mberthod/noisyless/01_PROJETS/202604_089_Capteur_Environnemental_V1/04_FABRICATION/PXL_20250319_190052271.MP.jpg

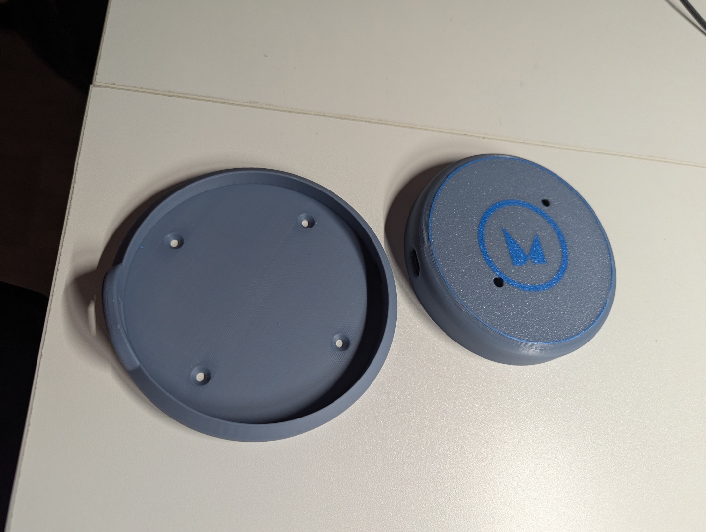
01_PROJETS/202604_089_Capteur_Environnemental_V1/04_FABRICATION/PXL_20250319_190052271.MP.jpg
