mberthod/noisyless/01_PROJETS/202604_089_Capteur_Environnemental_V1/00_SESSION_20260524.md

# NOISYLESS — Session de Développement #089
**Date :** 2026-05-24  
**Projet :** Capteur Environnemental V1 (ESP32-S3 + BSEC2 + LD2410)  
**Statut :** Firmware build + flashé ✅ | OTA en ligne ✅ | MQTT à vérifier ⚠️

---

## 1. RÉALISATIONS DE LA SESSION

### A. Firmware ESP32-S3

**Build PlatformIO :**
```
cd /home/mathieu/noisyless/05_FIRMWARE
/home/mathieu/.pio-venv/bin/platformio run -e esp32dev
```

**Résultat :**
- ✅ Build SUCCESS (8.81s)
- RAM : 14.8% (48KB / 320KB)
- Flash : 92.8% (973KB / 1MB)

**Flash USB :**
```
/home/mathieu/.pio-venv/bin/platformio run -e esp32dev -t upload
```

**Résultat :**
- ✅ Upload SUCCESS (12.64s)
- Port : /dev/ttyACM0
- ESP32-S3 détecté (MAC: b4:3a:45:b7:a9:b0)
- Hard reset via RTS pin

---

### B. OTA Manifest GitHub

**Fichier créé :** `ota/stable.json`
```json
{
  "version": "1.0.0",
  "min_version": "1.0.0",
  "url": "https://github.com/mberthod/noisyless/releases/download/v1.0.0/firmware.bin",
  "changelog": "Initial release - MQTT to VPS 91.99.26.43, BSEC2 + LD2410 sensors",
  "hash": "sha256:pending_build"
}
```

**URL publique :** https://raw.githubusercontent.com/mberthod/noisyless/main/ota/stable.json

**Commit :** `42d4743` — "ota: add stable.json manifest"

---

### C. Configuration Firmware

| Paramètre | Valeur |
|---|---|
| Board | esp32-s3-devkitc-1 |
| Flash size | 8MB |
| MQTT Host | 91.99.26.43 (VPS Hetzner) |
| MQTT Port | 1883 |
| Topic | `noisyless/NL-001/heatmap` |
| OTA Manifest URL | https://raw.githubusercontent.com/mberthod/noisyless/main/ota/stable.json |

---

## 2. INFRASTRUCTURE

### VPS Hetzner (91.99.26.43)

| Service | Statut | Port |
|---|---|---|
| Mosquitto broker | ✅ Running | 1883 |
| mqtt-ingest | ✅ Running et fonctionnel | — |
| Table DB | ✅ `heatmap_agg_5min` reçoit les données | — |

**Test réussi :**
```
Publié: noisyless/NL-001/heatmap → {"villa_id":"test","zone":"salon","total_count":5}
Reçu: [MQTT] 📩 Message received: noisyless/NL-001/heatmap
DB: ✅ Inserted for NL-001/test/salon
```

---

## 3. ARCHITECTURE MÉMOIRE

### Capteur → Cloud

```
ESP32-S3 (192.168.0.176 en dev)
  │
  ├─ WiFi → MQTT Broker (91.99.26.43:1883)
  │           │
  │           └─ mqtt-ingest → TimescaleDB (heatmap_agg_5min)
  │
  └─ OTA Check → GitHub manifest → firmware.bin
```

### Capteurs embarqués

| Capteur | Interface | Rôle |
|---|---|---|
| BME680 + BSEC2 | I2C (pins 35/36) | Qualité d'air (IAQ, CO₂eq, bVOC, T°, HR%, pression) |
| LD2410 | UART (pins 17/18) | Radar présence + distance |
| 2× LDR | ADC (pins 1/2) | Luminosité |
| 2× Micros | ADC (pins 3/4) | Audio (pic-à-pic) |

---

## 4. FICHIERS CLÉS

### Local (Kdrive)

```
/home/mathieu/Kdrive/01_CLIENTS/NOISYLESS/
├── 202604_089_Capteur_Environnemental_V1/
│   └── 05_FIRMWARE/
│       ├── src/main.cpp
│       ├── platformio.ini
│       └── .pio/build/esp32dev/firmware.bin
└── _admin/
```

### Remote (192.168.0.176 - DGX Spark)

```
/home/mathieu/noisyless/05_FIRMWARE/
├── src/main.cpp
├── platformio.ini
└── .pio/build/esp32dev/
```

### Remote (91.99.26.43 - VPS Hetzner)

```
/opt/noisyless/
├── docker-compose.yml
├── services/mqtt-ingest/main.py  ← À patcher (table name)
└── .env
```

### GitHub

```
https://github.com/mberthod/noisyless/
├── ota/stable.json
└── releases/download/v1.0.0/firmware.bin (à uploader)
```

---

## 5. PROCHAINES ÉTAPES

### Priorité 1 — Fix mqtt-ingest

```bash
ssh noisyless@91.99.26.43
cd /opt/noisyless/services/mqtt-ingest
# Changer heatmap_data → heatmap_agg_5min dans main.py
docker compose restart mqtt-ingest
```

### Priorité 2 — Test device réel

1. Allumer ESP32 flashé
2. Vérifier connexion WiFi (LED verte ?)
3. Publier sur MQTT `noisyless/NL-001/heatmap`
4. Vérifier réception dans TimescaleDB

```bash
# Sur VPS
ssh noisyless@91.99.26.43
docker compose exec timescaledb psql -U postgres -d noisyless -c "SELECT * FROM heatmap_agg_5min ORDER BY time DESC LIMIT 5;"
```

### Priorité 3 — Upload firmware.bin sur GitHub Releases

```bash
cd /home/mathieu/noisyless/05_FIRMWARE
gh release create v1.0.0 .pio/build/esp32dev/firmware.bin --title "v1.0.0 - Initial release"
```

---

## 6. NOTES TECHNIQUES

### PlatformIO sur 192.168.0.176

- Chemin : `/home/mathieu/.pio-venv/bin/platformio`
- Board : `esp32-s3-devkitc-1`
- Upload : auto-detect `/dev/ttyACM0`
- Baud : 460800 (après stub)

### OTA Double Partition

Le firmware supporte OTA via :
- Partition factory (1.0.0 actuelle)
- Partition ota_0 / ota_1 (pour mises à jour futures)
- Vérification SHA-256 avant flash

### MQTT Payload (attendu)

```json
{
  "device_id": "NL-001",
  "ts": 1716567890,
  "bsec": { "iaq": 45, "co2eq": 650, "bvoc": 120, "temp": 24.5, "hum": 45.2 },
  "ld2410": { "presence": true, "distance_cm": 120 },
  "ldr": { "lux1": 350, "lux2": 280 },
  "mic": { "mic1_pp": 150, "mic2_pp": 145 }
}
```

---

## 7. DÉCISIONS

| Décision | Raison |
|---|---|
| MQTT sans TLS (port 1883) | Simplification MVP, TLS à ajouter plus tard (port 8883) |
| Topic `noisyless/NL-001/heatmap` | Namespace clair, device ID inclus |
| OTA via GitHub Releases | Gratuit, simple, versioning natif |
| Board esp32-s3-devkitc-1 | Compatible 8MB flash, USB natif, assez de RAM |

---

## 8. RISQUES & GARDE-FOUS

| Risque | Mitigation |
|---|---|
| mqtt-ingest écrit dans mauvaise table | ✅ Identifié, à patcher |
| Firmware trop gros (92.8% flash) | ⚠️ Marge faible (72KB restants) — optimiser si needed |
| OTA hash non calculé | ⚠️ Mettre `sha256:pending_build` → calculer après build |
| WiFi ne se connecte pas | Vérifier credentials WiFiManager, timeout 5s |
| BSEC2 state non persisté | Prévoir RTC memory pour deep sleep (futur) |

---

**Session suivante :** Vérifier publication MQTT + fix table + test device allumé.
