mberthod/noisyless/.hermes/backlog/logs/2026-05-24_1519_fw-06.md

# Log fw-06 — 2026-05-24 15:19

**Tâche** : Créer la structure du firmware node-radar-60ghz : CMakeLists.txt, main/, components/

**Fichiers créés** :
- `firmware/node-radar-60ghz/CMakeLists.txt` — Projet ESP-IDF, EXTRA_COMPONENT_DIRS → components/
- `firmware/node-radar-60ghz/main/main.c` — Skeleton avec 3 tâches FreeRTOS (sensor_task, health_task, master_task), init NVS/netif/event-loop, timer périodique 1s, pins LED/ADC
- `firmware/node-radar-60ghz/main/CMakeLists.txt` — Composant ESP-IDF standard
- `firmware/node-radar-60ghz/components/` — Dossier vide, prêt pour ld6001a, mesh, config

**Détails main.c** :
- Inclusions complètes : freertos, esp_log, nvs_flash, esp_netif, esp_event, driver/gpio, driver/adc
- TODO placés stratégiquement aux points d'insertion pour ld6001a.h, mesh.h, config.h
- sensor_task : structure de lecture radar UART avec TODO pour ld6001a_read_frame()
- health_task : lecture ADC batterie, seuil critique 3000mV → deep sleep 10min
- master_task : skeleton avec TODO mesh_get_role() et fusion/publish MQTT
- app_main() : init LED, NVS, TCP/IP, crée les 3 tâches pinned core 0, timer 1s

**Modèle utilisé** : node-tof-esp32s3/main/main.c — mêmes tâches mais adapté pour radar (UART au lieu d'I²C, pas de grille ToF)

**Résultat** : ✅ Structure créée, 3 fichiers + dossier components vide. Prêt pour fw-07 (remplir main.c après drivers).
