mberthod/noisyless/.hermes/backlog/logs/2026-05-24_fw-01.md

# Log — fw-01 — 2026-05-24

## Tâche
**ID** : fw-01  
**Goal** : Tester le deep sleep sur le firmware #089  
**Priorité** : 3  

## Statut final
**BLOCKED** → Hardware ESP32-S3 non disponible.

## Raison
Le test de deep sleep nécessite :
- Une carte ESP32-S3 physique à flasher
- Un multimètre/analyseur de consommation pour mesurer la conso deep sleep (<100µA)
- Le firmware #089 prêt à être flashé

Hermes ne peut pas flasher physiquement ni mesurer la consommation réelle.

## Actions effectuées
- Tâche marquée `blocked` dans todo.json.

## Prochaine étape
Mathieu doit fournir le matériel et flasher manuellement.
