mberthod/noisyless/01_PROJETS/202604_089_Capteur_Environnemental_V1/01_CAHIER_DES_CHARGES/Cahiers des charges.odt

Cahiers des charges

# Objectifs du produit

Permettre de monitorer dans une location courte durée les différents paramètres environnementaux :

Parametre | objectif/explication | unité | Affichage ecran
Température | Indispensable pour le confort intérieur | mesuré en °C | oui
Humidité | Important pour le confort et le risque de croissance de moisissures | RH % | oui
Pression de l'air | En corrélation avec les changements météorologiques | Pa | oui
Résistance du capteur de gaz | Réagit aux impuretés chimiques organiques volatiles (COV) présentes dans l'air | ppm | oui
Indice de qualité de l'air | Combine le gaz, la température et l’humidité dans une évaluation de la qualité de l’air | Bon, moyen, mauvais | oui
Pression acoustique pondérée A | Niveau de pression acoustique (SPL) adapté à l'audition humaine | dB | non
Bande de fréquence SPL (x6) | Niveau de pression acoustique pour 6 bandes de fréquences, de 88 Hz à 5600 Hz | dB | non
Amplitude sonore maximale | La valeur en db des sons impulsifs soudains | dB | non
Éclairement | Luminosité totale, adaptée à la vision humaine | Lux | non
Niveau de lumière blanche | Luminosité totale sur toutes les longueurs d'onde mesurées | Lux | non

# Fonctionnement

le capteur est placé dans la ou les pièces du logement branché sur secteur

se connecte en wifi sur la box du logement ( a voir pour connexion 4G)

envoi sur le serveur de manière periodique les éléments le serveur gère les alertes

## Possibilités futures :

connexion 4G

fonctionnement sur batterie

Panneau de contrôle pour GAZ et qualité de l’air température avec un écran.

Ajout d’un carte micro sd pour logger les éléments en cas de coupure réseau et même coupure courant

# Block diagram

ALIMENTATION 230/5V ESP32 CAPTEUR BME680 - TEMPERATURE, HUMIDITE, PRESSION GAZ VEML6030 Ambient Light Sensor SPH0645LM4H-B MICROPHONE CHARGEUR BATTERIE ECRAN MODEM 4G SD CARD

# Budget électronique

Élément | Prix unitaire | Quantité
esp32S3 | 2,16 | 1
SPH0645LM4H-B | 1,5 | 1
BME680 | 7,4 | 1
VEML6030 | 1,20 | 1
Alimentation 85-240AC - 5VDC | 3 | 1
Écran | 3 | 1
Chargeur de batterie | 1 | 1
Batterie 500mA | 5 | 1
PCB | 5 | 1
| 38€

Version basique : 21€

Version haut de gamme : 31€

prix non optimisée en prod le prix sera inférieur

# Type de boîtier

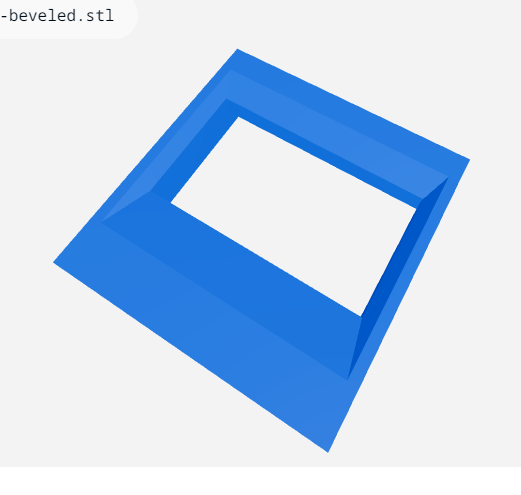
[picture p3: figure]
