mberthod/noisyless/.hermes/backlog/logs/2026-05-24_1545_web-02.md

# Log — web-02 — merci.html
**Timestamp**: 2026-05-24 15:45
**Tâche**: Créer la page /merci.html (confirmation de commande)
**Agent**: Hermes-MBHREP (orchestrateur backlog)
**Statut**: ✅ done

## Vérification
- Fichier: `/home/mathieu/Kdrive/01_CLIENTS/NOISYLESS/web/site/merci.html`
- Existe: ✅ OUI (87 lignes, 2606 bytes)
- Contenu: conforme au template NEWTODO.md section 1.4
  - `<meta name="robots" content="noindex">` ✅
  - Lecture params URL (name, email, session_id) ✅
  - Affichage dynamique via JS ✅
  - Style centré, simple ✅
  - Bouton "Retour au site" ✅
- Le fichier était déjà créé (probablement par un run précédent ou une création manuelle)

## Actions précises
- Aucune modification nécessaire — le fichier est conforme

## Fichiers modifiés
- Aucun (fichier déjà conforme)

## Résultat
- Tâche marquée "done" dans todo.json
- Page accessible à l'URL prévue
