mberthod/noisyless/.hermes/backlog/logs/2026-05-24_1615_web-03.md

# Log — web-03 : Page /annule.html (paiement annulé)

**Timestamp** : 2026-05-24 16:15 (estimé)
**Tâche** : Créer la page /annule.html (paiement annulé)
**Agent** : Hermes-MBHREP (orchestrateur backlog NOISYLESS)
**Statut** : ✅ Succès

## Actions précises

1. **Lu** `~/.hermes-mbhrep/backlog/todo.json` → détecté web-03 comme première tâche exécutable (priorité 1, status pending, après web-01 et web-02 déjà done)
2. **Marqué** `web-03` comme `in_progress`
3. **Lu** `NEWTODO.md` section 1.5 pour le contenu HTML exact
4. **Créé** le fichier `/home/mathieu/Kdrive/01_CLIENTS/NOISYLESS/web/site/annule.html` :
   - Contenu conforme exactement au template de NEWTODO.md
   - `<title>Paiement annulé | NOISYLESS</title>`
   - `<meta name="robots" content="noindex">` → pas d'indexation
   - Style inline centré, max-width 600px
   - Message : "Le paiement a été annulé. Aucun montant n'a été débité."
   - Lien "← Retour au site" vers `/`
5. **Marqué** `web-03` comme `done`

## Fichiers créés

- `~/Kdrive/01_CLIENTS/NOISYLESS/web/site/annule.html` : 15 lignes, 509 octets

## Résultat

✅ La page `/annule.html` est créée en tant que fichier statique, prête à être servie. Le lien depuis le checkout Stripe (cancel_url) pointera vers cette page.

## Notes

- Aucune dépendance backend, fichier HTML pur
- Le `noindex` empêche l'indexation par les moteurs de recherche
- La page est référencée dans `index.html` via la fonction `startCheckout()` (cancel_url)
