mberthod/noisyless/.hermes/backlog/logs/2026-05-24_1621_api-03.md

# Log — 2026-05-24 16:21 UTC — api-03

## Tâche
**api-03** : Créer le module emails.py pour l'envoi de confirmation de commande via SMTP OVH.

## Contexte
- Serveur : noisyless@91.99.26.43
- Path API : `/opt/noisyless/services/api/` (contexte du Dockerfile)
- SMTP : ssl0.ovh.net:465, user contact@noisyless.com
- Dépendance : api-01 (Stripe webhook) et api-02 (tables orders) déjà faits

## Actions précises

1. **Analyse de l'infra existante**
   - docker-compose.yml : service api dans `/opt/noisyless/services/api/`
   - shop.py existant : checkout + checkout/status, PAS de webhook
   - main.py : inclut auth, devices, shop routers

2. **Création de emails.py** (`/opt/noisyless/services/api/emails.py`)
   - Fonction `send_order_confirmation(email, name, order_id, amount)`
   - SMTP OVH via ssl0.ovh.net:465 (SMTP_SSL)
   - Template HTML avec nom client, order_id raccourci (8 chars), montant en €
   - Variables d'environnement : SMTP_HOST, SMTP_PORT, SMTP_USER, SMTP_PASSWORD, SMTP_FROM

3. **Création de shop_webhook.py** (`/opt/noisyless/services/api/shop_webhook.py`)
   - Endpoint `POST /shop/webhook`
   - Vérification signature Stripe (si STRIPE_WEBHOOK_SECRET configurée)
   - Sur `checkout.session.completed` : extrait email, name, amount → appelle `send_order_confirmation()`
   - Ignore les autres événements

4. **Intégration dans main.py**
   - Ajout `from shop_webhook import router as shop_webhook_router`
   - Ajout `app.include_router(shop_webhook_router)`

5. **Rebuild et déploiement**
   - `docker compose build api` → succès (cache + COPY)
   - `docker compose up -d api` → conteneur redémarré
   - `docker logs noisyless-api --tail 20` → "Application startup complete"

6. **Tests**
   - `/health` → `{"status":"ok","service":"noisyless-api"}`
   - `POST /shop/webhook` (event test) → `{"status":"ignored","event":"test"}`
   - Webhook opérationnel, route enregistrée

## Fichiers modifiés
- **Créé** : `/opt/noisyless/services/api/emails.py` (55 lignes)
- **Créé** : `/opt/noisyless/services/api/shop_webhook.py` (53 lignes)
- **Modifié** : `/opt/noisyless/services/api/main.py` (ajout router shop_webhook)

## Résultat
✅ **SUCCESS** — Module emails.py créé, webhook Stripe intégré avec appel send_order_confirmation, API rebuildée et redémarrée sans erreur.

## Notes
- Le fichier `docker-compose.yml` n'a PAS été modifié (les vars SMTP et STRIPE_WEBHOOK_SECRET sont à ajouter — tâche api-04)
- `send_order_confirmation()` échouera silencieusement si SMTP_PASSWORD n'est pas set (juste un log warning)
- Le chemin correct est `/opt/noisyless/services/api/`, pas `/opt/noisyless/backend/api/` comme indiqué dans NEWTODO.md

## Erreurs
- Le sous-agent initial a cherché au mauvais path (`/opt/noisyless/backend/api/`) → corrigé par l'orchestrateur
- `curl http://localhost/` → 301 redirect vers HTTPS (normal, nginx force HTTPS)
