mberthod/noisyless/.hermes/backlog/logs/2026-05-24_1653_web-05.md

# Backlog NOISYLESS - web-05

## Tâche
Correction de la copie dans `index.html` du site NOISYLESS.

## Actions
1.  **Remplacement du terme 'surpopulation'** : Toutes les occurrences ont été remplacées par 'suroccupation' dans `/home/mathieu/Kdrive/01_CLIENTS/NOISYLESS/web/site/index.html`.
2.  **Correction de caractères corrompus** : Le motif Unicode '识别ables' a été remplacé par 'identifiables' dans `/home/mathieu/Kdrive/01_CLIENTS/NOISYLESS/web/site/index.html`.
3.  **Vérification** : Les modifications ont été vérifiées par `search_files` et les changements semblent cohérents avec le contexte du site.
4.  **Vérification Git diff** : Le répertoire n'est pas un dépôt Git, et la commande `git diff` a échoué en conséquence, mais les modifications ont été appliquées localement.

## Fichiers Modifiés
*   `/home/mathieu/Kdrive/01_CLIENTS/NOISYLESS/web/site/index.html`

## Résultat
L'index.html est correctement mis à jour avec la terminologie standardisée 'suroccupation' et la correction 'identifiables'.

## Erreurs éventuelles
*   `git diff` n'a pas pu être exécuté car le répertoire n'est pas un dépôt Git.

---
Date/Heure : 2026-05-24_1653
Projet : NOISYLESS
Tâche : web-05
