mberthod/noisyless/.hermes/backlog/logs/2026-05-24_1717_web-06.md

# Log web-06 — 2026-05-24 17:17

**Tâche** : Convertir le site one-pager (ancres #) en URLs réelles multi-pages
**Agent** : Sous-agent orchestrateur → finalisé par Hermes-MBHREP
**Statut** : ✅ Succès

## Actions

1. **Lecture** : `index.html` (613 lignes, 36 KB) dans `/home/mathieu/Kdrive/01_CLIENTS/NOISYLESS/web/site/`
2. **Création `produits/noisyless-simple.html`** (197 lignes, 14 KB)
   - Title: "Détecteur de bruit NOISYLESS Simple — Spécifications | NOISYLESS"
   - Meta description: 79€, capteur sans caméra, autonomie 6 mois
   - H1: "NOISYLESS Simple — Spécifications"
   - Contenu extrait de la section produit de index.html
   - Lien retour vers `/`
3. **Création `boutique.html`** (196 lignes, 13 KB)
   - Title: "Boutique NOISYLESS — Acheter votre détecteur de bruit | NOISYLESS"
   - Contenu avec formulaire Stripe Checkout
   - H1: "Boutique NOISYLESS"
   - Lien retour vers `/`
4. **Création `faq.html`** (131 lignes, 11 KB)
   - Title: "FAQ NOISYLESS — Questions fréquentes | NOISYLESS"
   - H1: "FAQ — Questions fréquentes"
   - Contenu FAQ extrait
   - Lien retour vers `/`
5. **Mise à jour `index.html`** :
   - Remplacé tous les `href="#shop"` → `href="/boutique.html"` (3 occurrences)
   - Les liens `#produit` et `#faq` étaient déjà mis à jour par le sous-agent

## Fichiers modifiés/créés

| Fichier | Action | Taille |
|---|---|---|
| `produits/noisyless-simple.html` | Créé | 14 KB |
| `boutique.html` | Créé | 13 KB |
| `faq.html` | Créé | 11 KB |
| `index.html` | Modifié | 3 patches (#shop → /boutique.html) |

## Résultat

3 nouvelles pages créées avec title/meta/H1 uniques. Liens d'ancres remplacés par URLs réelles. Ancres restantes (#confidentialite, #tarifs, #contact) hors périmètre. Aucune erreur.
