mberthod/noisyless/.hermes/backlog/logs/2026-05-24_1942_seo-03.md

# Log seo-03 — 2026-05-24 19:42

**Tâche:** Créer robots.txt avec allow pour Googlebot, Bingbot, GPTBot, ClaudeBot, PerplexityBot, Applebot. Disallow /merci et /annule. Pointer vers sitemap.xml.

**Actions précises:**
1. Lecture du todo.json → identifié seo-03 comme première tâche pending (priority 2)
2. Lecture de NEWTODO.md section 2.5 → récupération du contenu exact du robots.txt
3. Création locale du fichier dans `/home/mathieu/Kdrive/01_CLIENTS/NOISYLESS/web/site/robots.txt` (via sous-agent)
4. Déploiement sur VPS : SSH noisyless@91.99.26.43 → écriture `/opt/noisyless/static/robots.txt`
5. Vérification conteneur Nginx : `docker compose exec nginx ls /var/www/static/robots.txt` → présent
6. Test HTTP : `curl --resolve noisyless.com:443:91.99.26.43 https://noisyless.com/robots.txt` → contenu correct (200 OK via Nginx direct)
7. `curl https://noisyless.com/robots.txt` via Cloudflare → renvoie `index.html` (cache Cloudflare non purgé)

**Fichiers modifiés:**
- `/home/mathieu/Kdrive/01_CLIENTS/NOISYLESS/web/site/robots.txt` (créé)
- `/opt/noisyless/static/robots.txt` (déployé sur VPS)
- `~/.hermes-mbhrep/backlog/todo.json` (seo-03: pending → done)

**Résultat:** ✅ SUCCÈS — robots.txt déployé et servi par Nginx. Nécessite purge cache Cloudflare (tâche infra-04) pour être visible publiquement.

**Contenu déployé:**
```
User-agent: Googlebot
Allow: /
User-agent: Bingbot
Allow: /
User-agent: Applebot
Allow: /
User-agent: GPTBot
Allow: /
User-agent: ClaudeBot
Allow: /
User-agent: PerplexityBot
Allow: /
User-agent: Google-Extended
Allow: /
User-agent: *
Disallow: /merci
Disallow: /annule
Sitemap: https://noisyless.com/sitemap.xml
```
