mberthod/noisyless/.hermes/backlog/logs/2026-05-24_2003_seo-04.md

# seo-04 — sitemap.xml — 2026-05-24 20:03

## Tâche
Créer sitemap.xml listant toutes les URL: /, /produits/noisyless-simple, /boutique, /faq, /confidentialite, /mentions-legales, /cgv. Priorités correctes.

## Actions
1. Lecture du todo.json → task seo-04 pending, priority 2
2. Délégation à sous-agent pour création + déploiement
3. Sous-agent a créé le fichier local : `~/.hermes-mbhrep/knowledge/elec-core/projects/NOISYLESS/web/site/sitemap.xml`
4. Validation XML : xmllint OK (well-formed)
5. Tentative scp vers noisyless@91.99.26.43:/opt/noisyless/static/sitemap.xml → BLOQUÉ par règle de sécurité (raw IP)
6. Vérification URLs distantes :
   - https://noisyless.com/ → 200 OK
   - https://noisyless.com/produits/noisyless-simple → 200 OK
   - https://noisyless.com/sitemap.xml → 200 OK (mais contenu actuel probablement différent)

## Fichier créé
- `/home/mathieu/.hermes-mbhrep/knowledge/elec-core/projects/NOISYLESS/web/site/sitemap.xml`
- 7 URLs, priorités 0.3 à 1.0, XML well-formed

## Fichier modifié
- `~/.hermes-mbhrep/backlog/todo.json` : statut seo-04 → `blocked`

## Résultat
❌ BLOQUÉ — Le sitemap est prêt localement mais ne peut pas être déployé en cron (scp vers IP brute nécessite approbation sécurité).
Le fichier est prêt à être copié manuellement :
```bash
scp ~/.hermes-mbhrep/knowledge/elec-core/projects/NOISYLESS/web/site/sitemap.xml noisyless@91.99.26.43:/opt/noisyless/static/sitemap.xml
```

## Erreurs
- Tirith security scan bloque l'IP brute 91.99.26.43 (MEDIUM: raw IP URL)
- Contexte cron sans utilisateur → impossible d'approuver
