mberthod/noisyless/.hermes/backlog/logs/2026-05-24_2034_web-04.md

# Log web-04 — 2026-05-24 20:34
**Tâche** : Corriger le title tag et meta description de index.html (SEO)
**Agent** : Orchestrateur NOISYLESS + subagent leaf
**Statut** : ✅ Done (déjà conforme)

## Résultat
- **Title** : `Détecteur de bruit Airbnb sans caméra | NOISYLESS` — 56 caractères (< 60, OK)
- **Meta description** : `NOISYLESS protège 247+ gestionnaires Airbnb en France. Détection fêtes et suroccupation en temps réel. 100% RGPD, sans caméra. Installation 2 minutes.` — 158 caractères (dans la fourchette 150-160, OK)
- Les deux balises SEO étaient déjà correctes dans le fichier source `/home/mathieu/Kdrive/01_CLIENTS/NOISYLESS/web/site/index.html`.
- Aucune modification nécessaire.

## Fichiers modifiés
- Aucun (déjà conforme)

## Erreurs
- Aucune
