mberthod/noisyless/.hermes/backlog/logs/2026-05-24_2050_seo-01.md

# Log seo-01 — 2026-05-24

**Timestamp:** 2026-05-24 20:50 (approx)
**Tâche:** seo-01 — Ajouter la section FAQ (6 questions) dans index.html avec balisage Schema.org FAQPage
**Statut:** ✅ done

## Actions précises

1. **Lu** `~/.hermes-mbhrep/backlog/todo.json` → identifié seo-01 comme première tâche pending (priorité 2)
2. **Marqué** `"status": "in_progress"` dans todo.json
3. **Lu** `~/Kdrive/01_CLIENTS/NOISYLESS/NEWTODO.md` → section 2.3 pour le code HTML exact
4. **Lu** `~/Kdrive/01_CLIENTS/NOISYLESS/web/site/index.html` → repéré le point d'insertion entre la section CTA (ligne 829) et le footer
5. **Inséré** la section FAQ complète avec 6 questions dans index.html :
   - Comment installer les capteurs ?
   - Est-ce conforme au RGPD ?
   - Quelle est l'autonomie des capteurs ?
   - Peut-on détecter une fête ?
   - Quels sont les capteurs disponibles ?
   - Y a-t-il un abonnement ?
6. **Ajouté** `itemscope itemtype="https://schema.org/FAQPage"` sur le conteneur `<section>`
7. **Ajouté** le CSS pour la section `.faq` (80px padding, style accordéon avec +/- toggle, bordures, typo)

## Fichiers modifiés

- `~/Kdrive/01_CLIENTS/NOISYLESS/web/site/index.html` : +48 lignes HTML (FAQ) + 52 lignes CSS

## Résultat

- ✅ 6 questions visibles avec balisage Schema.org complet (itemscope/itemprop/itemtype)
- ✅ CSS responsive pour l'accordéon FAQ
- ✅ FAQPage Schema prêt pour Google Rich Results Test
- Fichier `index.html` passé de 901 à ~1003 lignes

## Erreurs

Aucune.
