mberthod/noisyless/.hermes/backlog/logs/2026-05-24_2101_seo-07.md

Summary log for SEO-07 campaign:

**Tâche :** Création et déploiement de la page FAQ enrichie pour NOISYLESS.
**Objectif :** Produire un fichier faq.html optimisé (2000+ mots, schéma JSON-LD) contenant 11 questions enrichies, le déployer sur le serveur 91.99.26.43, vérifier son accessibilité, et archiver le résumé.
**Timestamp :** 2026-05-24_2101

**Actions effectuées :**
1.  **Analyse Préalable :** Le fichier `index.html` était manquant. Le fichier `faq.html` existait localement (chemin : `./Kdrive/01_CLIENTS/NOISYLESS/web/site/faq.html`), servant de base stylistique.
2.  **Création du Contenu :** Un nouveau fichier `faq.html` a été créé localement dans `/home/mathieu/.hermes-mbhrep/knowledge/elec-core/projects/NOISYLESS/web/site/faq.html`. Le contenu a été enrichi pour dépasser le seuil des 2000 mots en développant chaque réponse FAQ, tout en maintenant la structure SEO (JSON-LD, titre, méta-description) et le style cohérent avec les ressources existantes.
3.  **Déploiement (Attempt):** Une tentative a été effectuée de déployer le fichier vers le serveur `91.99.26.43` via `scp`.
    *   **Résultat :** Les tentatives de déploiement ont échoué ou ont été interceptées par des vérifications de sécurité en raison de l'utilisation d'adresses IP brutes. Le déploiement physique du fichier a échoué et n'est donc pas confirmé.
4.  **Vérification d'Accessibilité (Attempt):** Une tentative de vérification via `curl -I` a été effectuée.
    *   **Résultat :** Cette vérification a également échoué pour la même raison sécuritaire (utilisation d'une IP brute). L'accessibilité n'a pu être vérifiée.

**Fichiers Modifiés :**
*   `/home/mathieu/.hermes-mbhrep/knowledge/elec-core/projects/NOISYLESS/web/site/faq.html` (Création/Écrasement)

**Résultat Global :**
*   Le fichier `faq.html` est créé et enrichi localement avec un contenu qualitatif de plus de 2000 mots, 13 questions/FAQ, et un balisage FAQPage JSON-LD complet.
*   **Avertissement :** Les étapes de déploiement sur le serveur `91.99.26.43` et la vérification de l'accessibilité en ligne ont échoué techniquement. Le déploiement et la vérification doivent être réessayés manuellement ou en utilisant le nom de domaine plutôt que l'adresse IP directe, car les outils automatiques rejettent les adresses IP brutes pour des raisons de sécurité.
*   Le fichier est prêt à être téléversé par un autre canal de déploiement si nécessaire.
