mberthod/noisyless/.hermes/backlog/logs/2026-05-24_infra-04.md

# Log — infra-04 — 2026-05-24

## Tâche
**ID** : infra-04  
**Goal** : Purger le cache Cloudflare après tous les déploiements web  
**Priorité** : 2  

## Statut final
**BLOCKED** → @Mathieu doit le faire manuellement.

## Raison
Aucune API key Cloudflare n'est configurée. Cette tâche nécessite un accès au dashboard Cloudflare (cloudflare.com → Caching → Purge Everything). Hermes ne peut pas interagir avec l'interface web Cloudflare.

## Actions effectuées
- Aucune action automatisable possible.
- Tâche marquée `blocked` dans todo.json.

## Prochaine étape
Mathieu doit se connecter manuellement sur https://dash.cloudflare.com et purger le cache après les déploiements.
