mberthod/noisyless/01_PROJETS/202605_091_HeatMap_Presence/_commun/deployment/roadmap.md

# NOISYLESS — Roadmap produit & commercialisation 2026

**North Star :** contribution à l'objectif **+200 000 € de revenu personnel** (décembre 2026).
**Horizon contraint :** ~7 mois (mai → décembre 2026).
**Règle de tri :** ce qui génère du cash *avant* décembre prime. Tout hardware neuf nécessitant certification ou outillage = revenu 2027, pas 2026.
**Périmètre :** ce roadmap couvre la ligne NOISYLESS + protection immobilier. C'est une **part** du North Star, pas la totalité — ELEC-CORE (régie), HEXACORE et les autres BU contribuent en parallèle.

---

## Principe directeur

Vendre et étendre l'existant (logiciel-driven), **pas** concevoir du hardware neuf.
> « Conduire la Tesla à pleine vitesse, ne pas empiler des sprints d'infrastructure. »

---

## Écosystème produit

**Socle commun :** gateway de flotte (cellular + WiFi) + dashboard multi-biens (SaaS).

- **NOISYLESS (base)** — bruit + qualité d'air, WiFi. *Existe, en commercialisation.*
- **NOISYLESS EVENT** — fusion anti-soirée + comptage radar + détection vapotage + cellular autonome (indépendant du WiFi locataire).
- **Protection du bien (2027+)** — coupure d'eau automatique, squat/intrusion, hors-gel, etc.

---

## Phase 1 — Cash immédiat (juin → juillet 2026)

Activer le revenu sur l'existant, zéro dépendance hardware.

- [ ] Pousser la vente du **NOISYLESS base** (0 dev) — prospection active conciergeries + villas premium
- [ ] **Dashboard fleet MVP** — vue multi-biens, historique horodaté
- [ ] Feature **export preuve juridique** (rapport opposable pour retenue de caution)
- [ ] Mise en place de l'**abonnement SaaS** (MRR) + ligne cellular facturée

**KPI :** premiers deals signés · MRR > 0 · pipeline conciergerie ouvert.

---

## Phase 2 — Montée en gamme & flotte (août → septembre 2026)

- [ ] **NOISYLESS EVENT — firmware de fusion** : CO2 / SPL / comptage / PM-VOC, machine à états + hystérésis (tolérance zéro faux positif)
- [ ] Intégrer radar 60 GHz + module cellular sur la plateforme existante
- [ ] **Closer 2-3 deals conciergerie/gestionnaire** (hardware multi-unités + SaaS) — le vrai multiplicateur
- [ ] Grille tarifaire : base / EVENT / abonnement flotte

**KPI :** EVENT en pré-commande · deals flotte en cours de signature.

---

## Phase 3 — Scale & atterrissage (octobre → décembre 2026)

- [ ] Livraison **EVENT** + upsell base → EVENT
- [ ] Déploiement flotte sur les deals signés
- [ ] **Seed dev coupure d'eau** (specs + proto) — financé par le cash 2026, livré 2027

**KPI :** objectif de contribution annuelle de la ligne atteint.

---

## Modèle de revenu (à caler avec tes prix réels)

Trois leviers, à additionner :

1. **Ventes unitaires** = (unités base × prix) + (unités EVENT × prix premium)
2. **Deals flotte** = nb gestionnaires × (unités/contrat × prix) — c'est ici que le volume se fait
3. **Récurrent** = (abonnement SaaS + ligne cellular) × nb unités actives × nb mois

> Le hardware seul ne tient pas l'objectif. La combinaison **deals flotte + MRR** est ce qui rend les 200k atteignables. À chiffrer dès que la grille tarifaire est figée (Phase 2).

---

## 2027 — Échelle (financée par le cash 2026)

- **Coupure d'eau automatique** (inline + clamp-on retrofit) → **canal assurance B2B2C** = volume. Sinistre n°1 habitation FR.
- **Détection squat/intrusion** — extension rapide d'EVENT (présence + cellular déjà présents).

---

## Hors-scope / différé (Tier 3)

Features de gamme, pas des moteurs de chiffre dans la fenêtre 2026 :
détecteur fumée+CO (cert EN 14604 trop lourde), point chaud tableau, bris de vitre, anti-moisissure, radon, monitoring conso élec/eau.

---

## Arbitrage ouvert (à trancher avant fin juin)

**EVENT maintenant** (effort firmware, upsell à forte marge) **vs 100 % vente du NOISYLESS base d'abord** (zéro dev, cash immédiat) ?
