mberthod/noisyless/01_PROJETS/202605_091_HeatMap_Presence/_commun/deployment/blog/channel-managers-monitoring.md

---
title: "Channel managers (Guesty, Smoobu, Lodgify) : intégrer le monitoring"
description: "Intégrer un capteur de bruit à son channel manager (Guesty, Smoobu, Lodgify) automatise les alertes et la communication voyageur. Voici comment connecter le monitoring à votre flux de gestion."
slug: channel-managers-monitoring
date: 2026-05-24
author: L'équipe NOISYLESS
keywords: [guesty capteur bruit, smoobu monitoring, lodgify intégration, channel manager location courte durée]
---

# Channel managers (Guesty, Smoobu, Lodgify) : intégrer le monitoring

**Intégrer un capteur de bruit à un channel manager comme Guesty, Smoobu ou Lodgify permet d'automatiser les alertes et la communication avec le voyageur depuis un seul flux de gestion. L'objectif : déclencher un message au-delà d'un seuil sonore sans intervention humaine, et centraliser les incidents par logement.**

Pour un gestionnaire de parc, le monitoring n'a de valeur que s'il s'intègre au quotidien — là où sont déjà gérées les réservations, les arrivées et les messages.

## Pourquoi connecter le monitoring au channel manager

- **Réponse automatique** : un dépassement de seuil peut déclencher un message pré-rédigé au voyageur, via la messagerie de la plateforme.
- **Centralisation** : les incidents remontent par logement, à côté des réservations, sans jongler entre outils.
- **Traçabilité** : chaque alerte est horodatée et rattachée au séjour concerné.
- **Passage à l'échelle** : indispensable dès que l'on gère plus de quelques biens.

## Comment se fait l'intégration

Deux approches courantes :

1. **Webhooks** : le capteur (ou sa plateforme) envoie un événement à une URL, qui déclenche une action dans le channel manager ou un outil d'automatisation.
2. **API REST** : pour lire les mesures et piloter les alertes depuis votre propre système.

Côté NOISYLESS, l'offre Pro expose **webhooks et API REST**, ce qui permet de brancher les alertes sur Guesty, Smoobu, Lodgify ou un outil d'automatisation intermédiaire (type Zapier/Make) selon vos besoins.

> Vérifiez les connecteurs disponibles côté channel manager : les capacités d'intégration évoluent régulièrement.

## Un protocole de réponse graduée

L'intégration prend tout son sens avec une escalade : premier seuil → message automatique au voyageur ; seuil persistant → notification au gestionnaire ; dépassement prolongé → consignation pour preuve. Le tout sans intervention humaine sur les premiers paliers.

## Avec NOISYLESS

L'abonnement [Pro](/#tarifs) inclut webhooks, intégrations et alertes Telegram/SMS, en plus du dashboard multi-biens. De quoi connecter le monitoring à votre stack de gestion existante.

## FAQ

**NOISYLESS s'intègre-t-il à Guesty ou Smoobu ?**
Via webhooks et API REST (offre Pro), les alertes peuvent être connectées à un channel manager directement ou via un outil d'automatisation. Vérifiez les connecteurs disponibles côté plateforme.

**Faut-il un développeur pour l'intégration ?**
Pas nécessairement : un outil no-code (Zapier, Make) peut relier les webhooks à la plupart des channel managers.

**Quel intérêt pour un seul logement ?**
L'intégration est surtout utile à l'échelle d'un parc. Pour un bien isolé, les alertes email/push natives suffisent souvent.

---

*Voir aussi : [Minut vs NOISYLESS](/blog/minut-vs-noisyless-comparatif) · [Détecter une fête sans caméra](/blog/detecter-fete-airbnb-sans-camera)*

<!-- JSON-LD -->
<script type="application/ld+json">
{
  "@context": "https://schema.org",
  "@type": "FAQPage",
  "mainEntity": [
    { "@type": "Question", "name": "NOISYLESS s'intègre-t-il à Guesty ou Smoobu ?", "acceptedAnswer": { "@type": "Answer", "text": "Via webhooks et API REST (offre Pro), les alertes peuvent être connectées à un channel manager directement ou via un outil d'automatisation." } },
    { "@type": "Question", "name": "Faut-il un développeur pour l'intégration ?", "acceptedAnswer": { "@type": "Answer", "text": "Pas nécessairement : un outil no-code comme Zapier ou Make peut relier les webhooks à la plupart des channel managers." } }
  ]
}
</script>
