mberthod/noisyless/01_PROJETS/202605_091_HeatMap_Presence/_commun/deployment/blog/degat-des-eaux-vanne-coupure-automatique.md

---
title: "Dégât des eaux en location : prévention par vanne de coupure automatique"
description: "Le dégât des eaux est le premier sinistre en habitation. Un détecteur de fuite couplé à une vanne motorisée coupe l'eau automatiquement en quelques secondes et limite les dégâts."
slug: degat-des-eaux-vanne-coupure-automatique
date: 2026-05-24
author: L'équipe NOISYLESS
keywords: [détecteur fuite eau location, vanne coupure automatique, prévention dégât des eaux, capteur fuite airbnb]
---

# Dégât des eaux en location : prévention par vanne de coupure automatique

**Le dégât des eaux est le sinistre le plus fréquent en habitation. Dans une location, où le logement est souvent inoccupé entre deux séjours, une fuite peut couler des heures avant d'être découverte. Un détecteur de fuite couplé à une vanne motorisée coupe l'arrivée d'eau automatiquement en quelques secondes, transformant un sinistre majeur en simple incident.**

Une canalisation qui lâche, un raccord de lave-linge qui cède, un ballon d'eau chaude qui fuit : sans personne sur place, les conséquences s'aggravent à chaque heure.

## Pourquoi la location est particulièrement exposée

- **Vacance fréquente** entre les réservations : personne pour réagir.
- **Rotation des occupants** : usage intensif et imprévisible des équipements.
- **Distance du propriétaire** : le gestionnaire est rarement à proximité immédiate.

Le délai de découverte est le facteur n°1 du coût d'un dégât des eaux. Le réduire à quelques secondes change tout.

## Comment fonctionne la coupure automatique

Le principe est simple et robuste :

1. Une **sonde** détecte la présence d'eau là où elle ne devrait pas être (sous l'évier, près du ballon, du lave-linge).
2. Le système déclenche une **vanne motorisée** placée sur l'arrivée d'eau.
3. L'eau est **coupée en quelques secondes**, avant que la fuite ne se propage.
4. Une **alerte** (push, email) prévient le gestionnaire.

Un point technique important : une vanne à mécanisme auto-bloquant **reste fermée même en cas de coupure de courant**, et le dispositif doit pouvoir actionner la fermeture sur batterie de secours — car une fuite peut survenir pendant une panne électrique.

## L'intérêt assurantiel

Réduire le risque de dégât des eaux est un argument auprès des assureurs : la prévention diminue la sinistralité. Pour un gestionnaire de parc, équiper les logements d'une coupure automatique est un investissement qui se rentabilise dès le premier sinistre évité.

## Avec NOISYLESS

Le [Détecteur de Fuite + Vanne](/produits/detecteur-fuite) associe détection d'eau instantanée et vanne motorisée avec coupure automatique en moins de 5 secondes, plus alerte push et email. Il complète la gamme de monitoring sur le même dashboard.

## FAQ

**La vanne reste-t-elle fermée en cas de coupure de courant ?**
Oui, avec un mécanisme auto-bloquant : la position fermée est maintenue sans alimentation, et la fermeture peut être déclenchée sur batterie de secours.

**Faut-il un plombier pour l'installer ?**
Cela dépend du modèle : certaines versions se posent en ligne sur l'arrivée d'eau (intervention plombier), d'autres en rénovation simplifiée.

**Combien de temps pour couper l'eau après une fuite ?**
Quelques secondes — moins de 5 secondes pour le module NOISYLESS — contre potentiellement plusieurs heures sans dispositif.

---

*Voir aussi : [Minut vs NOISYLESS](/blog/minut-vs-noisyless-comparatif) · [Nuisances sonores et copropriété](/blog/nuisances-sonores-copropriete)*

<!-- JSON-LD -->
<script type="application/ld+json">
{
  "@context": "https://schema.org",
  "@type": "FAQPage",
  "mainEntity": [
    { "@type": "Question", "name": "La vanne reste-t-elle fermée en cas de coupure de courant ?", "acceptedAnswer": { "@type": "Answer", "text": "Oui, avec un mécanisme auto-bloquant : la position fermée est maintenue sans alimentation, et la fermeture peut être déclenchée sur batterie de secours." } },
    { "@type": "Question", "name": "Combien de temps pour couper l'eau après une fuite ?", "acceptedAnswer": { "@type": "Answer", "text": "Quelques secondes — moins de 5 secondes pour le module NOISYLESS — contre potentiellement plusieurs heures sans dispositif." } }
  ]
}
</script>
