mberthod/noisyless/01_PROJETS/202605_091_HeatMap_Presence/_commun/deployment/blog/detecter-fete-airbnb-sans-camera.md

---
title: "Comment détecter une fête dans une location Airbnb sans caméra"
description: "Détecter une fête sans caméra repose sur la fusion de capteurs : niveau sonore, montée de CO₂ et comptage de présence. Voici comment repérer une soirée à temps."
slug: detecter-fete-airbnb-sans-camera
date: 2026-05-24
author: L'équipe NOISYLESS
keywords: [détecter fête airbnb, solution anti-fête location, capteur soirée airbnb, surveillance sans caméra]
---

# Comment détecter une fête dans une location Airbnb sans caméra

**Pour détecter une fête sans caméra, on combine trois signaux : le niveau sonore, la montée du taux de CO₂ et le comptage de présence. Pris isolément, chacun peut tromper ; fusionnés, ils révèlent une soirée ou une suroccupation de façon fiable et sans aucune atteinte à la vie privée.**

Une caméra est interdite à l'intérieur d'une location. La bonne nouvelle : on n'en a pas besoin. Une fête laisse des traces physiques mesurables bien avant que le voisinage ne se plaigne.

## Les trois signaux d'une fête

- **Le bruit.** Un niveau sonore élevé et soutenu (au-delà d'un seuil en dB, sur une durée) est le signal le plus évident.
- **Le CO₂.** Chaque personne expire du CO₂. Une montée rapide du taux dans une pièce trahit un afflux de monde — y compris quand la musique est encore basse, en début de soirée.
- **Le comptage de présence.** Un capteur de distance (ToF) ou un radar compte le nombre de personnes réellement présentes, sans les identifier.

## Pourquoi la fusion change tout

Le bruit seul génère des faux positifs : un aspirateur, un sèche-cheveux, un enfant qui crie. Le CO₂ seul monte aussi avec une simple cuisson. Mais **quand les trois signaux convergent** — niveau sonore soutenu + CO₂ qui grimpe + nombre de personnes au-dessus de la limite du contrat — la probabilité d'une vraie soirée devient très élevée. C'est cette logique de fusion qui réduit les fausses alertes.

## Agir avant le voisinage

L'intérêt du dispositif est la **prévention** : une alerte de premier seuil permet d'envoyer un message au voyageur pour rappeler les règles, souvent suffisant pour calmer la situation. Si le dépassement persiste, l'historique horodaté constitue une preuve objective, utile en cas de litige ou de retenue de caution — sans jamais avoir enregistré image ni son.

## Avec NOISYLESS

Le capteur [NOISYLESS Simple](/produits/noisyless-simple) mesure le bruit, la présence et le CO₂ sur un seul boîtier. Pour le comptage précis du nombre de personnes, le module [HeatMap Intérieur](/produits/heatmap-interieur) ajoute une matrice ToF 16×16. L'ensemble remonte en temps réel sur le dashboard, avec des alertes graduées.

## FAQ

**Un capteur de CO₂ peut-il vraiment détecter du monde ?**
Oui. Le CO₂ expiré par les occupants fait monter le taux ambiant ; une hausse rapide est un indicateur fiable d'afflux de personnes.

**Comment éviter les fausses alertes ?**
En croisant plusieurs signaux (bruit, CO₂, présence) plutôt qu'un seul, et en appliquant des seuils sur une durée plutôt qu'instantanés.

**Est-ce légal ?**
Oui, tant qu'aucune caméra ni aucun micro d'enregistrement n'est utilisé et que le dispositif est mentionné dans l'annonce. Voir [notre article sur la légalité](/blog/detecteur-bruit-airbnb-legal).

---

*Voir aussi : [Suroccupation : la repérer légalement](/blog/suroccupation-location-courte-duree) · [Nuisances sonores et copropriété](/blog/nuisances-sonores-copropriete)*

<!-- JSON-LD -->
<script type="application/ld+json">
{
  "@context": "https://schema.org",
  "@type": "FAQPage",
  "mainEntity": [
    { "@type": "Question", "name": "Un capteur de CO₂ peut-il détecter du monde ?", "acceptedAnswer": { "@type": "Answer", "text": "Oui. Le CO₂ expiré par les occupants fait monter le taux ambiant ; une hausse rapide est un indicateur fiable d'afflux de personnes." } },
    { "@type": "Question", "name": "Comment éviter les fausses alertes ?", "acceptedAnswer": { "@type": "Answer", "text": "En croisant plusieurs signaux (bruit, CO₂, présence) plutôt qu'un seul, et en appliquant des seuils sur une durée." } }
  ]
}
</script>
