mberthod/noisyless/01_PROJETS/202605_091_HeatMap_Presence/_commun/deployment/blog/detecteur-bruit-airbnb-legal.md

---
title: "Un détecteur de bruit est-il légal en location Airbnb ? (2026)"
description: "Oui, un détecteur de bruit est légal en location Airbnb s'il n'enregistre aucun son et s'il est mentionné dans l'annonce. Les caméras intérieures, elles, sont interdites."
slug: detecteur-bruit-airbnb-legal
date: 2026-05-24
author: L'équipe NOISYLESS
keywords: [détecteur de bruit airbnb légal, capteur bruit location RGPD, caméra interdite airbnb, obligation information locataire]
---

# Un détecteur de bruit est-il légal en location Airbnb ?

**Oui, un détecteur de bruit est légal en location Airbnb en France, à deux conditions : il ne doit ni enregistrer ni transmettre de son, et sa présence doit être clairement mentionnée dans l'annonce. À l'inverse, toute caméra à l'intérieur du logement est strictement interdite par les plateformes.**

La distinction tient en une phrase : mesurer un niveau sonore n'est pas écouter. Un capteur conforme calcule une intensité en décibels (dB) ; il ne capte jamais le contenu d'une conversation. C'est ce qui le rend compatible avec le RGPD et avec les règles d'Airbnb.

## Ce que dit Airbnb

Airbnb autorise les dispositifs de surveillance du bruit à condition qu'ils soient signalés dans l'annonce et qu'ils ne portent pas atteinte à la vie privée des voyageurs. La plateforme interdit en revanche, sans exception, les caméras et tout dispositif d'enregistrement à l'intérieur du logement. Un capteur de bruit qui ne fait que mesurer des décibels reste donc dans le cadre autorisé.

## Ce que dit le RGPD

Le règlement européen protège les données à caractère personnel. Or, un niveau sonore exprimé en dB, sans enregistrement audio, n'identifie personne : il ne constitue pas une donnée permettant de reconnaître un individu. Deux principes restent à respecter :

- **Transparence** : informer le voyageur de la présence et de la finalité du dispositif (prévenir les nuisances, pas surveiller les personnes).
- **Minimisation** : ne collecter que la donnée strictement utile — ici, le niveau sonore et, le cas échéant, une présence binaire ou une mesure de qualité d'air.

Un capteur sans micro et sans caméra coche naturellement ces deux cases.

## La caméra : la ligne rouge

C'est le point sur lequel les hôtes se font sanctionner. Toute caméra intérieure est interdite, même éteinte, même annoncée. La seule technologie d'occupation autorisée à l'intérieur est celle qui ne produit pas d'image : un capteur de présence (PIR), un capteur de distance (ToF) ou un radar produisent des grilles de distances ou des points, jamais une image identifiable.

## Comment rester 100 % conforme

1. Choisir un capteur **sans micro ni caméra**, qui mesure uniquement le niveau sonore en dB (idéalement selon la norme IEC 61672-1).
2. **Mentionner le dispositif dans l'annonce** et dans le règlement intérieur du logement.
3. Privilégier un fournisseur dont les **données sont hébergées dans l'Union européenne**, avec un DPO désigné.
4. Configurer une **alerte de prévention** : prévenir le voyageur avant que le voisinage ne réagisse.

Les capteurs [NOISYLESS](/produits/noisyless-simple) mesurent le niveau sonore en dB SPL (IEC 61672-1 classe 2), sans micro ni caméra, avec un hébergement en Europe et un DPO désigné — un cadre pensé pour rester conforme par construction.

> Cet article est informatif et ne constitue pas un conseil juridique. Pour une situation précise, consultez un professionnel.

## FAQ

**Un détecteur de bruit enregistre-t-il les conversations ?**
Non, s'il est conforme : il mesure une intensité en décibels et ne capte pas le contenu audio. Il est donc impossible de réécouter une conversation.

**Faut-il prévenir le voyageur ?**
Oui. L'information préalable, dans l'annonce et le règlement intérieur, est une condition de conformité.

**Peut-on installer une caméra discrète à la place ?**
Non. Toute caméra intérieure est interdite par Airbnb et expose l'hôte à la suspension de son annonce.

---

*Voir aussi : [Comment détecter une fête sans caméra](/blog/detecter-fete-airbnb-sans-camera) · [RGPD et capteurs en location : guide de conformité](/blog/rgpd-capteurs-location-conformite)*

<!-- JSON-LD à placer dans le <head> de la page -->
<script type="application/ld+json">
{
  "@context": "https://schema.org",
  "@graph": [
    {
      "@type": "Article",
      "headline": "Un détecteur de bruit est-il légal en location Airbnb ?",
      "author": { "@type": "Organization", "name": "NOISYLESS" },
      "datePublished": "2026-05-24",
      "about": "Légalité des détecteurs de bruit en location courte durée"
    },
    {
      "@type": "FAQPage",
      "mainEntity": [
        { "@type": "Question", "name": "Un détecteur de bruit enregistre-t-il les conversations ?", "acceptedAnswer": { "@type": "Answer", "text": "Non, s'il est conforme : il mesure une intensité en décibels et ne capte pas le contenu audio. Il est impossible de réécouter une conversation." } },
        { "@type": "Question", "name": "Faut-il prévenir le voyageur ?", "acceptedAnswer": { "@type": "Answer", "text": "Oui. L'information préalable, dans l'annonce et le règlement intérieur, est une condition de conformité." } },
        { "@type": "Question", "name": "Peut-on installer une caméra discrète à la place ?", "acceptedAnswer": { "@type": "Answer", "text": "Non. Toute caméra intérieure est interdite par Airbnb et expose l'hôte à la suspension de son annonce." } }
      ]
    }
  ]
}
</script>
