mberthod/noisyless/01_PROJETS/202605_091_HeatMap_Presence/_commun/deployment/blog/minut-vs-noisyless-comparatif.md

---
title: "Minut vs NOISYLESS : comparatif 2026 et alternatives"
description: "Comparatif des détecteurs de bruit pour Airbnb : Minut, NOISYLESS et alternatives. Bruit, occupation, qualité d'air, hébergement des données et prix passés au crible."
slug: minut-vs-noisyless-comparatif
date: 2026-05-24
author: L'équipe NOISYLESS
keywords: [minut vs noisyless, alternative minut, détecteur de bruit airbnb comparatif, meilleur capteur bruit location]
---

# Minut vs NOISYLESS : comparatif 2026 et alternatives

**Minut est le détecteur de bruit historique du marché Airbnb, centré sur le son, le mouvement et la température. NOISYLESS ajoute la qualité d'air, le comptage d'occupation par capteur ToF et radar, un hébergement des données en Europe, et une gamme qui couvre aussi la fuite d'eau. Le bon choix dépend de ce que vous voulez réellement détecter.**

> Les caractéristiques et tarifs des produits concurrents évoluent. Vérifiez les chiffres sur les sites officiels avant publication ou décision d'achat.

## Tableau comparatif

| Critère | Minut | NOISYLESS |
|---|---|---|
| Niveau sonore (dB) | Oui | Oui — dB SPL IEC 61672-1 classe 2 |
| Détection présence / mouvement | Oui | Oui (PIR) |
| Comptage d'occupation | Limité | Oui — ToF 16×16 et radar 60 GHz |
| Qualité d'air (CO₂, T°, humidité) | Partiel | Oui |
| Détection fuite d'eau + vanne | Non | Oui (produit dédié) |
| Hébergement des données | À vérifier | Europe (OVH France + TimescaleDB Allemagne) |
| Sans caméra ni micro | Oui | Oui |
| Dashboard multi-biens | Oui | Oui |
| Prix d'entrée | À vérifier | 79 € + abonnement dès 4,99 €/mois |

## Les forces de Minut

Minut est l'acteur établi, reconnu sur le marché de la location courte durée, avec une application mature et des automatisations d'alerte au voyageur. Pour un hôte qui veut uniquement surveiller le bruit avec une solution éprouvée, c'est une référence solide.

## Ce que NOISYLESS apporte en plus

- **Comptage d'occupation fiable en appartement.** Les solutions qui détectent l'occupation via le WiFi des téléphones échouent en immeuble (elles captent les voisins). Les capteurs ToF et radar de NOISYLESS mesurent une présence réelle dans la pièce.
- **Qualité d'air intégrée.** Le CO₂ est un excellent indicateur de suroccupation : une montée rapide signale un afflux de personnes, même silencieux.
- **Données en Europe.** Serveurs OVH (France) et base TimescaleDB (Allemagne), aucun transfert hors UE, DPO désigné — un argument de conformité pour les conciergeries.
- **Au-delà du bruit.** La gamme couvre aussi la prévention des dégâts des eaux avec un [détecteur de fuite à coupure automatique](/blog/degat-des-eaux-vanne-coupure-automatique).

## Et les autres alternatives ?

D'autres dispositifs existent : certains misent sur l'occupation détectée par WiFi (efficaces en maison isolée, peu fiables en appartement), d'autres sur des rapports PDF quotidiens de niveau sonore. Le critère décisif reste le même : que voulez-vous détecter — uniquement le bruit, ou aussi l'occupation réelle, la qualité d'air et les risques matériels ?

## Conclusion

Pour du monitoring sonore simple et éprouvé, Minut fait le travail. Pour une vision complète du logement — bruit, occupation réelle, qualité d'air, fuite d'eau — avec des données hébergées en Europe, [NOISYLESS](/produits/noisyless-simple) couvre un périmètre plus large sur une seule plateforme.

## FAQ

**NOISYLESS est-il compatible avec un appartement en copropriété ?**
Oui. Contrairement aux solutions basées sur la détection WiFi, ses capteurs ToF et radar mesurent une présence réelle dans la pièce, sans confondre avec les voisins.

**Où sont hébergées les données de NOISYLESS ?**
En Europe : serveurs OVH en France et base de données en Allemagne, sans transfert hors UE.

**Quelle solution choisir pour un parc de logements ?**
Les deux proposent un dashboard multi-biens. Pour un gestionnaire, l'hébergement européen et le comptage d'occupation fiable en appartement sont des critères discriminants.

---

*Voir aussi : [Comment détecter une fête sans caméra](/blog/detecter-fete-airbnb-sans-camera) · [Suroccupation : la repérer légalement](/blog/suroccupation-location-courte-duree)*

<!-- JSON-LD à placer dans le <head> -->
<script type="application/ld+json">
{
  "@context": "https://schema.org",
  "@type": "FAQPage",
  "mainEntity": [
    { "@type": "Question", "name": "NOISYLESS est-il compatible avec un appartement en copropriété ?", "acceptedAnswer": { "@type": "Answer", "text": "Oui. Ses capteurs ToF et radar mesurent une présence réelle dans la pièce, sans confondre avec les voisins, contrairement aux solutions WiFi." } },
    { "@type": "Question", "name": "Où sont hébergées les données de NOISYLESS ?", "acceptedAnswer": { "@type": "Answer", "text": "En Europe : serveurs OVH en France et base de données en Allemagne, sans transfert hors UE." } }
  ]
}
</script>
