mberthod/noisyless/01_PROJETS/202605_091_HeatMap_Presence/_commun/deployment/blog/nuisances-sonores-copropriete.md

---
title: "Nuisances sonores et copropriété : ce que risque votre annonce"
description: "En copropriété, les nuisances sonores d'une location courte durée peuvent entraîner plaintes du syndic, procédures et suspension de l'annonce. Voici les risques et comment s'en prémunir."
slug: nuisances-sonores-copropriete
date: 2026-05-24
author: L'équipe NOISYLESS
keywords: [nuisances sonores copropriété, airbnb syndic, suspension annonce airbnb, règlement copropriété location courte durée]
---

# Nuisances sonores et copropriété : ce que risque votre annonce

**En copropriété, les nuisances sonores répétées d'une location courte durée exposent l'hôte à des plaintes du voisinage et du syndic, à des procédures, et à la suspension voire la fermeture de son annonce par la plateforme. La prévention par un capteur de bruit est devenue le principal moyen de protéger son activité.**

Le marché de la location courte durée s'est fortement professionnalisé, et la tolérance des syndics a chuté. Une seule soirée mal gérée peut suffire à enclencher une spirale coûteuse.

## Les risques concrets

- **Plaintes et mise en demeure** du voisinage ou du syndic, parfois suivies d'un rappel au règlement de copropriété.
- **Procédure** : en cas de troubles répétés, le syndicat des copropriétaires peut engager une action, et certains règlements limitent ou interdisent la location courte durée.
- **Suspension de l'annonce** : les plateformes sanctionnent les hôtes en cas de manquements répétés aux règles, pouvant aller jusqu'à l'interdiction de publier.
- **Coût direct** : frais de ménage, dégradations, et surtout perte de revenus si l'activité est suspendue.

> Cet article est informatif et ne remplace pas un conseil juridique adapté à votre règlement de copropriété.

## Ce que dit (souvent) le règlement de copropriété

Beaucoup de règlements contiennent une clause de jouissance paisible interdisant les troubles anormaux de voisinage, dont le bruit. Certains encadrent explicitement la location meublée de courte durée. Lire son règlement est la première étape : il définit ce qui est autorisé et les recours du syndic.

## Se prémunir : la prévention plutôt que la sanction

L'enjeu n'est pas de surveiller les voyageurs mais de **réagir avant le voisinage**. Un capteur de bruit qui alerte dès le dépassement d'un seuil permet d'envoyer un message au voyageur et de calmer la situation en amont. En cas de litige, l'historique horodaté fournit une preuve objective, sans image ni enregistrement sonore.

## Avec NOISYLESS

[NOISYLESS](/produits/noisyless-simple) mesure le niveau sonore en dB et déclenche des alertes graduées, avec un historique exploitable comme preuve. Conçu sans caméra ni micro et hébergé en Europe, il reste conforme aux règles d'Airbnb et au RGPD.

## FAQ

**Le syndic peut-il interdire ma location Airbnb ?**
Selon le règlement de copropriété et la réglementation locale, la location courte durée peut être encadrée ou interdite. Vérifiez votre règlement.

**Un historique de bruit est-il une preuve recevable ?**
Un relevé horodaté de niveaux sonores constitue un élément factuel utile, notamment pour justifier une intervention ou une retenue de caution. Sa valeur dépend du contexte.

**Comment éviter les plaintes du voisinage ?**
En étant alerté tôt grâce à un capteur, en informant clairement les voyageurs des règles, et en réagissant dès le premier dépassement.

---

*Voir aussi : [Un détecteur de bruit est-il légal ?](/blog/detecteur-bruit-airbnb-legal) · [Détecter une fête sans caméra](/blog/detecter-fete-airbnb-sans-camera)*

<!-- JSON-LD -->
<script type="application/ld+json">
{
  "@context": "https://schema.org",
  "@type": "FAQPage",
  "mainEntity": [
    { "@type": "Question", "name": "Le syndic peut-il interdire ma location Airbnb ?", "acceptedAnswer": { "@type": "Answer", "text": "Selon le règlement de copropriété et la réglementation locale, la location courte durée peut être encadrée ou interdite. Vérifiez votre règlement." } },
    { "@type": "Question", "name": "Un historique de bruit est-il une preuve recevable ?", "acceptedAnswer": { "@type": "Answer", "text": "Un relevé horodaté de niveaux sonores est un élément factuel utile, notamment pour justifier une intervention ou une retenue de caution." } }
  ]
}
</script>
