mberthod/noisyless/01_PROJETS/202605_091_HeatMap_Presence/_commun/deployment/blog/vapotage-cigarette-location-detection.md

---
title: "Vapotage et cigarette en location : comment les détecter"
description: "La fumée de cigarette et le vapotage se détectent sans caméra grâce aux capteurs de particules fines (PM2.5) et de composés organiques volatils (COV). Voici comment faire respecter le non-fumeur."
slug: vapotage-cigarette-location-detection
date: 2026-05-24
author: L'équipe NOISYLESS
keywords: [détecter cigarette location, capteur vapotage airbnb, détection fumée non-fumeur, pm2.5 cov location]
---

# Vapotage et cigarette en location : comment les détecter

**La fumée de cigarette et le vapotage se détectent sans caméra grâce aux capteurs de particules fines (PM2.5) et de composés organiques volatils (COV). Leur signature combinée permet de distinguer un épisode de tabac ou de vape d'une simple cuisson, et d'alerter en temps réel pour faire respecter une règle non-fumeur.**

Une location annoncée non-fumeur qui sent le tabac, c'est un nettoyage en profondeur, des avis négatifs et parfois un séjour à reloger. Le détecter sur le moment permet d'agir et de justifier des frais.

## Pourquoi la détection est possible sans caméra

Fumer ou vapoter libère dans l'air des marqueurs mesurables :

- **Particules fines (PM2.5)** : la fumée de cigarette en génère un pic caractéristique.
- **Composés organiques volatils (COV)** : la vape, qui produit peu de particules classiques, se trahit surtout par une signature de COV.

Aucun de ces capteurs ne capte image ni son : ils mesurent la composition de l'air, ce qui les rend conformes au RGPD.

## Distinguer le tabac de la cuisine

Le défi technique est d'éviter les fausses alertes : une cuisson génère aussi des particules. La solution est la **fusion de signaux** — croiser le profil PM2.5 et COV, leur dynamique de montée et leur durée — pour isoler la signature propre au tabac ou à la vape. Un seul capteur suffit rarement ; c'est la combinaison qui fiabilise.

## Faire respecter la règle non-fumeur

Comme pour le bruit, l'approche gagnante est la prévention et la preuve :

- **Alerte en temps réel** dès qu'une signature de fumée est détectée.
- **Historique horodaté** pour justifier, le cas échéant, des frais de remise en état prévus dans les conditions de séjour.
- **Mention dans l'annonce** du caractère non-fumeur et de la présence d'un capteur de qualité d'air.

## Avec NOISYLESS

Le capteur [NOISYLESS Simple](/produits/noisyless-simple) intègre la mesure de qualité d'air (CO₂, température, humidité). La détection fine de la signature tabac/vape repose sur la combinaison de capteurs PM2.5 et COV — un axe de la gamme de monitoring environnemental NOISYLESS.

## FAQ

**Peut-on détecter le vapotage, qui fait peu de fumée ?**
Oui, principalement via les composés organiques volatils (COV) : la vape produit peu de particules classiques mais une signature COV détectable.

**Comment éviter de confondre avec la cuisine ?**
En croisant plusieurs signaux (PM2.5, COV, dynamique et durée) plutôt qu'un seuil unique, pour isoler la signature propre au tabac ou à la vape.

**Est-ce légal de détecter la fumée en location ?**
Oui : un capteur de qualité d'air ne capte ni image ni son. Comme tout dispositif, il doit être mentionné dans l'annonce.

---

*Voir aussi : [RGPD et capteurs en location](/blog/rgpd-capteurs-location-conformite) · [Détecter une fête sans caméra](/blog/detecter-fete-airbnb-sans-camera)*

<!-- JSON-LD -->
<script type="application/ld+json">
{
  "@context": "https://schema.org",
  "@type": "FAQPage",
  "mainEntity": [
    { "@type": "Question", "name": "Peut-on détecter le vapotage, qui fait peu de fumée ?", "acceptedAnswer": { "@type": "Answer", "text": "Oui, principalement via les composés organiques volatils (COV) : la vape produit peu de particules classiques mais une signature COV détectable." } },
    { "@type": "Question", "name": "Comment éviter de confondre avec la cuisine ?", "acceptedAnswer": { "@type": "Answer", "text": "En croisant plusieurs signaux (PM2.5, COV, dynamique et durée) plutôt qu'un seuil unique, pour isoler la signature propre au tabac ou à la vape." } }
  ]
}
</script>
