mberthod/noisyless/01_PROJETS/202604_089_Capteur_Environnemental_V1/01_CAHIER_DES_CHARGES/image5.png

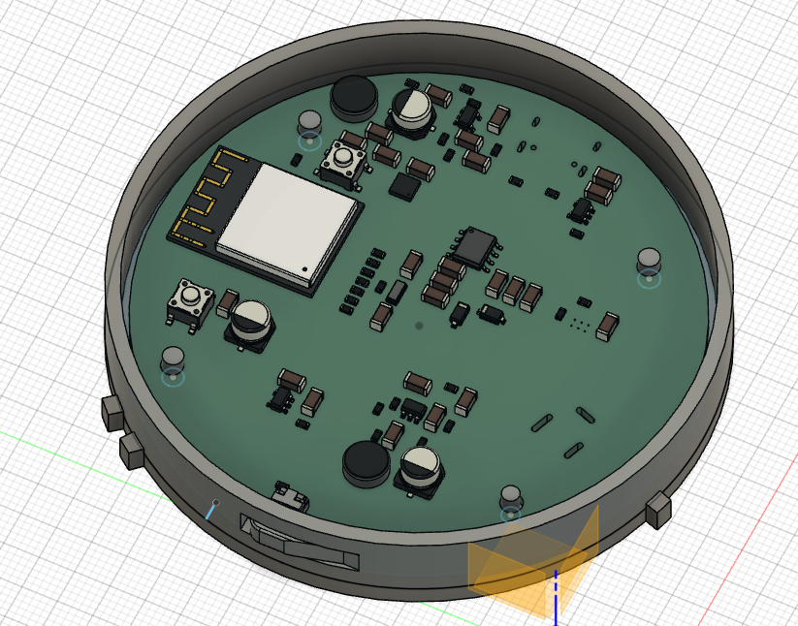
01_PROJETS/202604_089_Capteur_Environnemental_V1/01_CAHIER_DES_CHARGES/image5.png
