mberthod/noisyless/01_PROJETS/202605_091_HeatMap_Presence/hardware/kicad/MCU.kicad_sch

## KiCad design 01_PROJETS/202605_091_HeatMap_Presence/hardware/kicad/MCU.kicad_sch (2026-05-26)

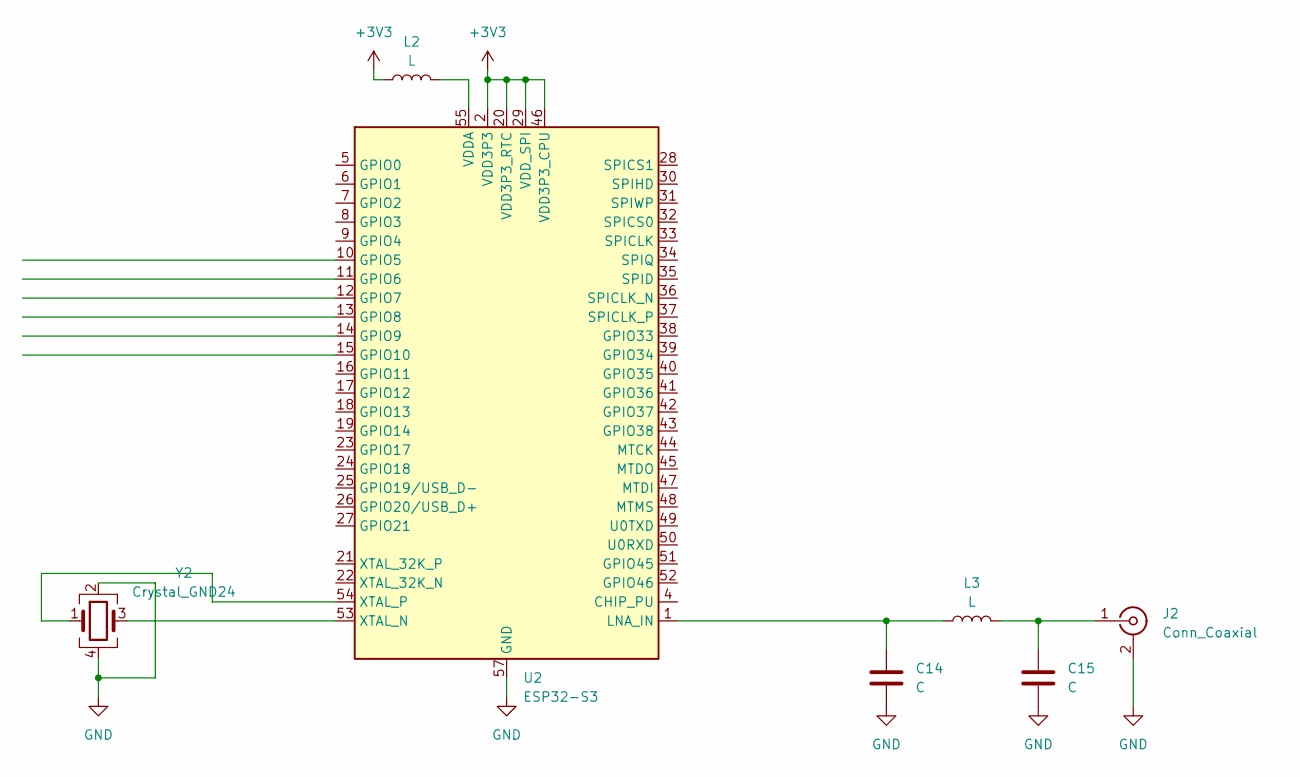
[picture p20: schematic MCU.kicad_sch]

Parts:
C14, C15: C
J2: Conn_Coaxial; U.FL_Hirose_U.FL-R-SMT-1_Vertical
L2: L; L_0805_2012Metric
L3: L
U2: ESP32-S3; QFN-56-1EP_7x7mm_P0.4mm_EP4x4mm
Y2: Crystal_GND24

Connections:
+3V3: L2.1, U2.2 (VDD3P3), U2.3 (VDD3P3), U2.20 (VDD3P3_RTC), U2.29 (VDD_SPI), U2.46 (VDD3P3_CPU)
GND: C14.2, C15.2, J2.2 (Ext), U2.57 (GND), Y2.2, Y2.4
unnamed: C14.1, L3.1, U2.1 (LNA_IN)
unnamed: C15.1, J2.1 (In), L3.2
unnamed: L2.2, U2.55 (VDDA), U2.56 (VDDA)
unnamed: U2.53 (XTAL_N), Y2.3
unnamed: U2.54 (XTAL_P), Y2.1
