mberthod/noisyless/05_FIRMWARE/include/credentials.h

#pragma once

// Secrets MQTT (placés dans un fichier ignoré par le VCS)
static const char* MQTT_HOST = "91.99.26.43";   // VPS NOISYLESS (Hetzner)
static const uint16_t MQTT_PORT = 1883;
static const char* MQTT_USER = "esp32";
static const char* MQTT_PASS = "am#k^keu5nBDWLB";
